TheBadZhang/PD24/software/src/common.h

#ifndef __TBZ_COMMON_H__
#define __TBZ_COMMON_H__

#ifdef __cplusplus
extern "C" {
#endif

#include "main.h"

extern ADC_HandleTypeDef hadc1;
extern SPI_HandleTypeDef hspi1;
// extern UART_HandleTypeDef huart2;
extern I2C_HandleTypeDef hi2c1;
extern I2C_HandleTypeDef hi2c2;


extern TIM_HandleTypeDef htim3;
extern TIM_HandleTypeDef htim16;
extern TIM_HandleTypeDef htim17;

#ifdef __cplusplus
}
#endif

#endif
